gianlucag/LastWord/hardware/schematic.kicad_sch

## KiCad design hardware/schematic.kicad_sch (2026-09-12)

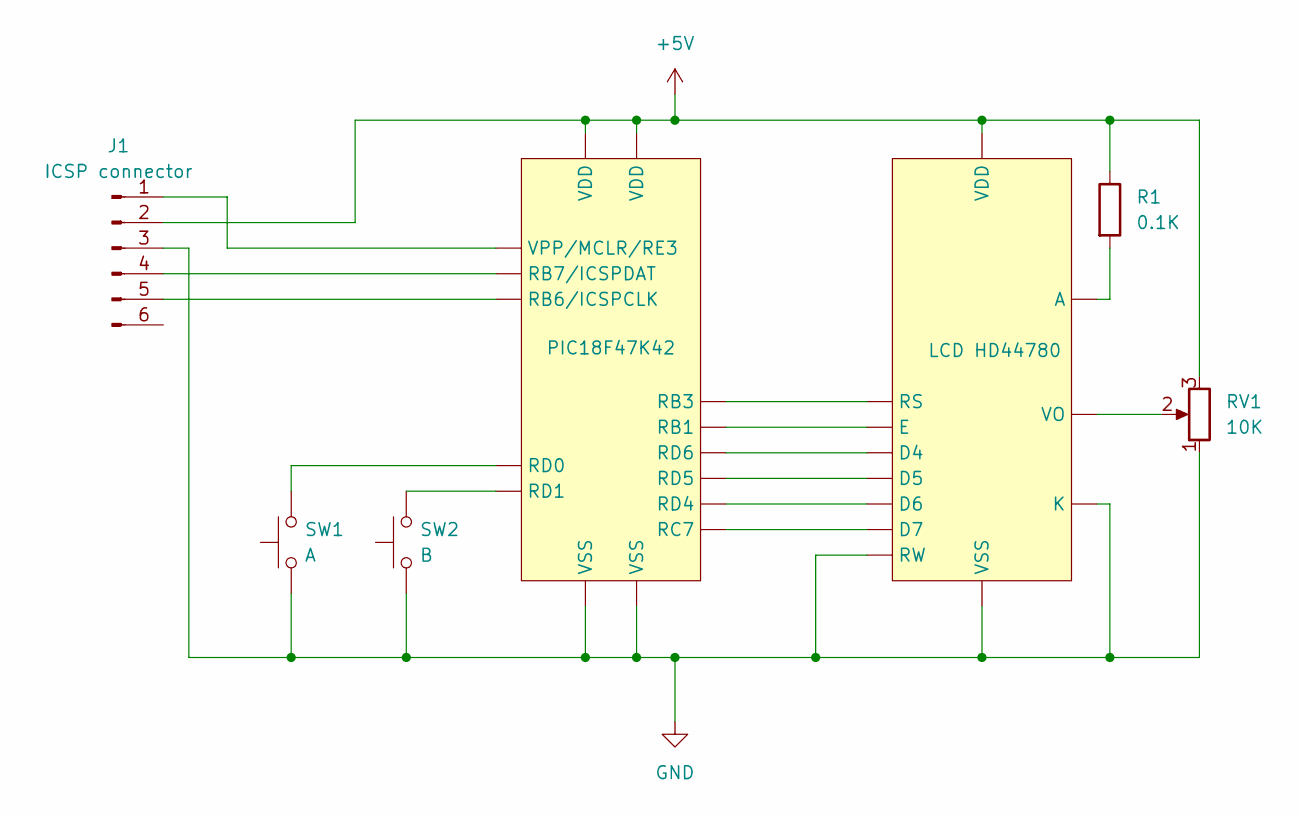
[picture p7: schematic schematic.kicad_sch]

Parts:
J1: ICSP connector
R1: 0.1K
RV1: 10K
SW1: A
SW2: B
U1: PIC18F47K42; DIP-40_W15.24mm
U2: LCD HD44780; DIP-40_W15.24mm

Connections:
+5V: J1.2, R1.1, RV1.3, U1., U2.
GND: J1.3, RV1.1, SW1.1, SW2.1, U1., U2.
unnamed: J1.1, U1.
unnamed: J1.4, U1.
unnamed: J1.5, U1.
unnamed: R1.2, U2.
unnamed: RV1.2, U2.
unnamed: SW1.2, U1.
unnamed: SW2.2, U1.
unnamed: U1., U2.
