gianlucag/LastWord/firmware/about.h

/*
*******************************************************************************
 About

 Show firmware information
*******************************************************************************
*/

#ifndef ABOUT_H
#define ABOUT_H

void about_run(void);

#endif
