gianlucag/LastWord/firmware/board_emulator.c

/*
*******************************************************************************
 Board

 Emulator implementation
*******************************************************************************
*/

#include "board.h"

void board_init(void)
{
}
