gianlucag/LastWord/firmware/delay.h

/*
*******************************************************************************
 Delay

 Millisecond and microsecond delay routines
*******************************************************************************
*/

#ifndef DELAY_H
#define DELAY_H

#include <stdint.h>

void delay_us(uint16_t us);
void delay_ms(uint16_t ms);

#endif
