gianlucag/LastWord/firmware/entropy_input.h

/*
*******************************************************************************
 Entropy input

 Acquires entropy supplied by the user and encodes it as a BIP-39 mnemonic
*******************************************************************************
*/

#ifndef ENTROPY_INPUT_H
#define ENTROPY_INPUT_H

void entropy_input_run(void);

#endif
