gianlucag/LastWord/firmware/menu.h

/*
*******************************************************************************
 Menu

 Main menu
*******************************************************************************
*/

#ifndef MENU_H
#define MENU_H

void menu_run(void);

#endif
