gianlucag/LastWord/firmware/splash.h

/*
*******************************************************************************
 Splash screen

 Shows name and version on screen
*******************************************************************************
*/

#ifndef SPLASH_H
#define SPLASH_H

void splash_show(void);

#endif
