gianlucag/LastWord/firmware/self_test.h

/*
*******************************************************************************
 Self test

 Run the tests and show results
*******************************************************************************
*/

#ifndef SELF_TEST_H
#define SELF_TEST_H

void self_test_run(void);
void self_test_boot(void);

#endif
