gianlucag/LastWord/firmware/tests.h

/*
*******************************************************************************
 Tests

 Unit tests
*******************************************************************************
*/

#ifndef TESTS_H
#define TESTS_H

#include <stdint.h>

uint8_t test_run(void); // 1 = 100% pass, 0 = some tests failed

#endif
